fabriziofiorucci/Compact-Weather-Station/pics/raw_IMG_20211016_144026-thumb.jpg

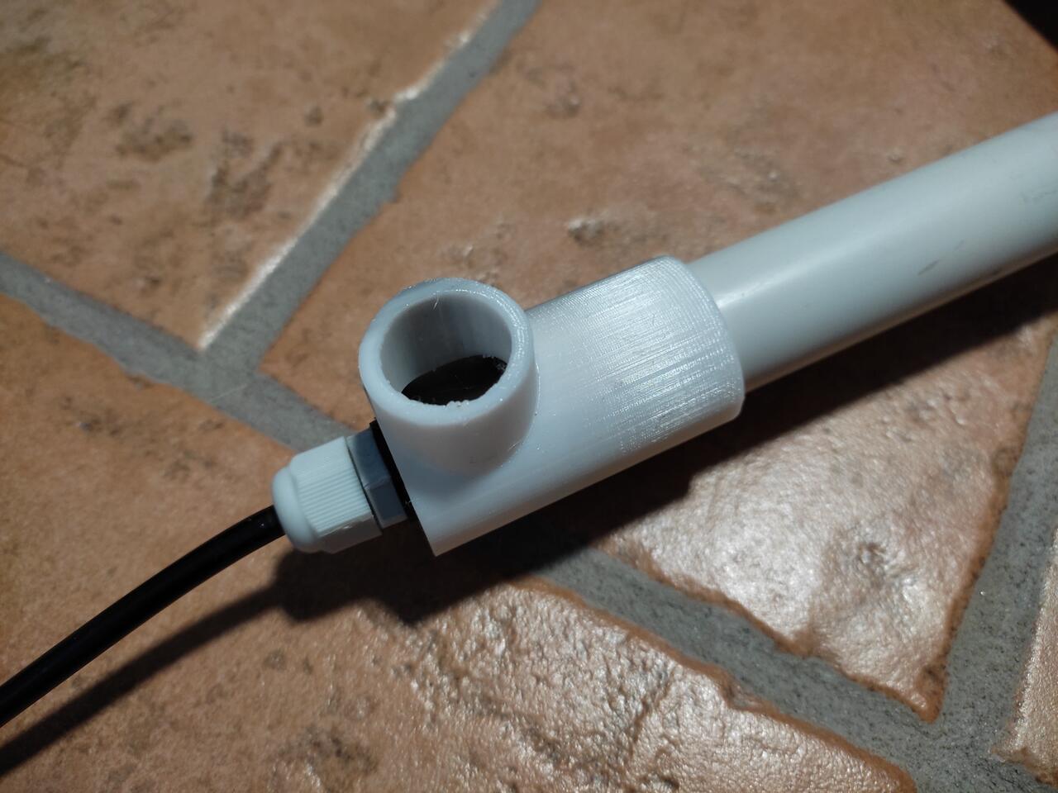
pics/raw_IMG_20211016_144026-thumb.jpg
