fabriziofiorucci/Compact-Weather-Station/pics/raw_IMG_20211016_144029-thumb.jpg

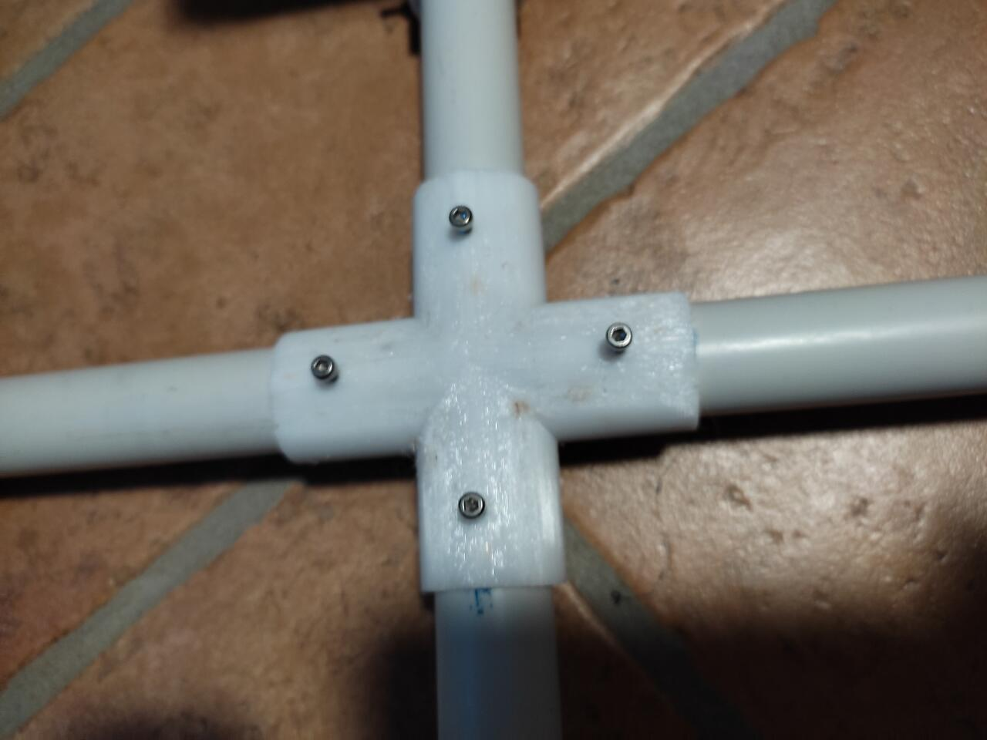
pics/raw_IMG_20211016_144029-thumb.jpg
