fabriziofiorucci/Compact-Weather-Station/pics/raw_IMG_20211016_221820-thumb.jpg

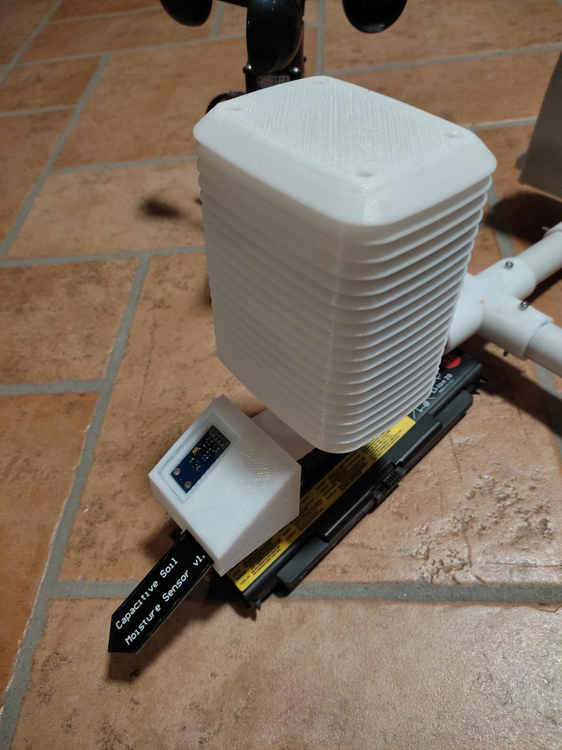
pics/raw_IMG_20211016_221820-thumb.jpg
